ZHJ0125/FrequencyMeter/Image/00_频率计原理.jpg

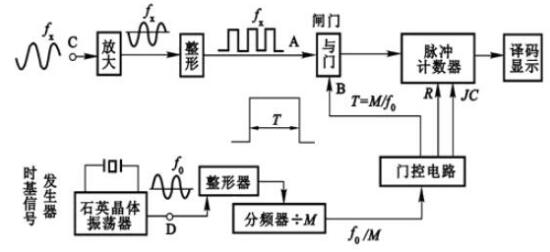
Image/00_频率计原理.jpg
