ZHJ0125/FrequencyMeter/Image/38_编译错误.png

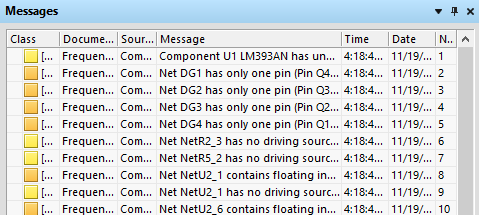
Image/38_编译错误.png
