ZHJ0125/FrequencyMeter/Image/95_生成PDF.png

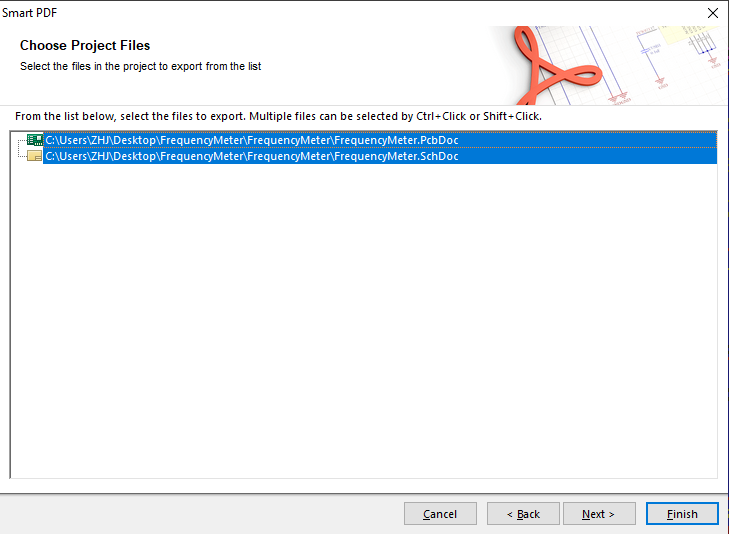
Image/95_生成PDF.png
