ZHJ0125/FrequencyMeter/Image/96_生成原理图PDF.png

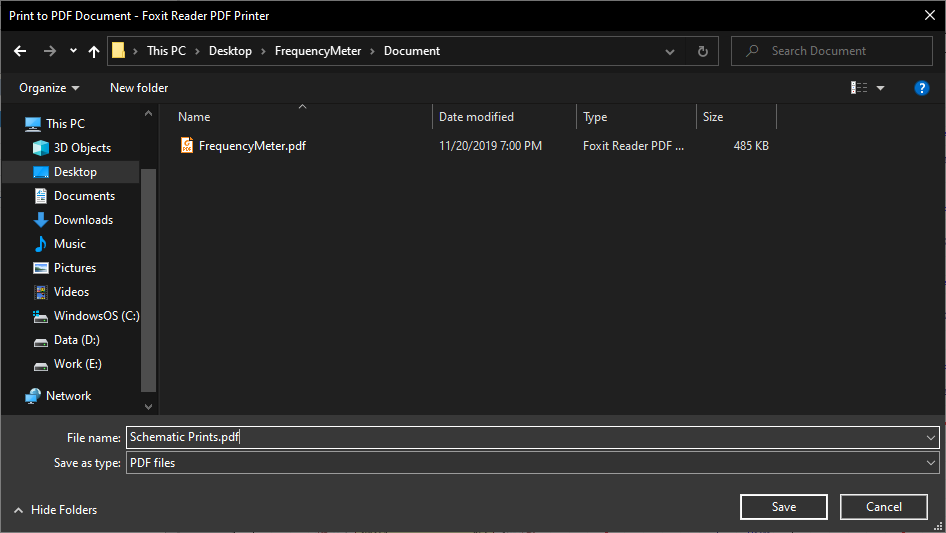
Image/96_生成原理图PDF.png
