ZHJ0125/FrequencyMeter/Image/98_文件规格.png

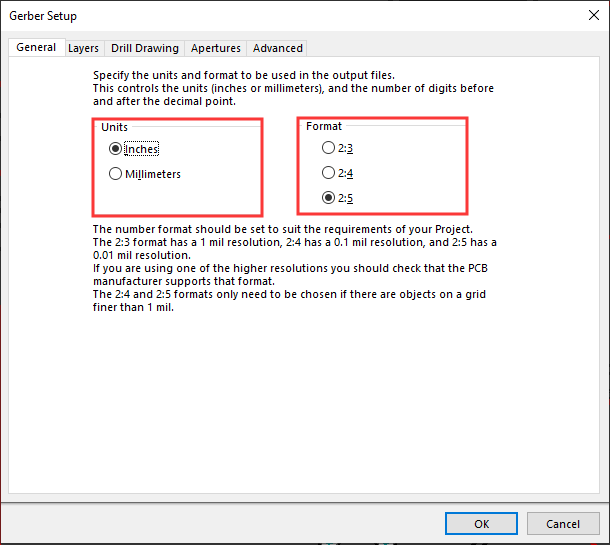
Image/98_文件规格.png
