ZHJ0125/FrequencyMeter/Image/99_版层输出.png

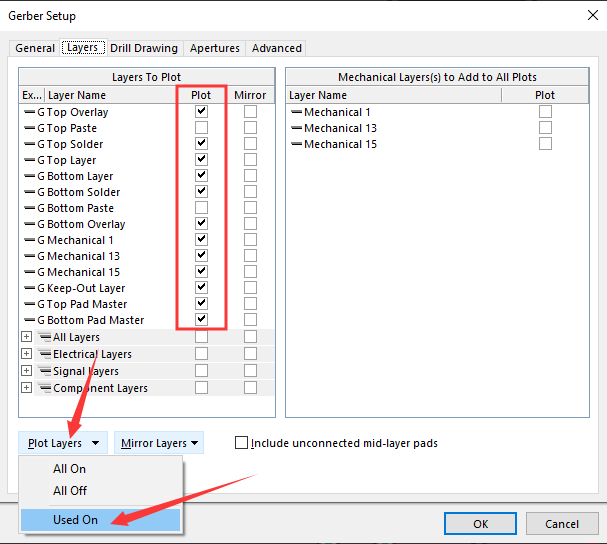
Image/99_版层输出.png
