ZHJ0125/FrequencyMeter/Image/100_输出设置.png

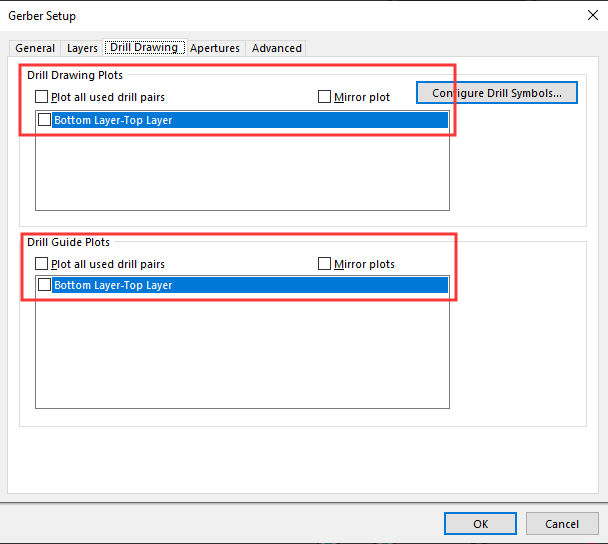
Image/100_输出设置.png
