ZHJ0125/FrequencyMeter/Image/101_嵌入式孔径.png

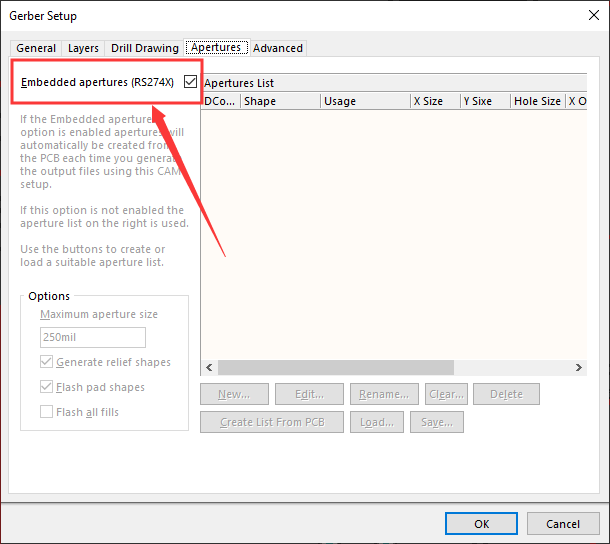
Image/101_嵌入式孔径.png
