ZHJ0125/FrequencyMeter/Image/102_高级设置.png

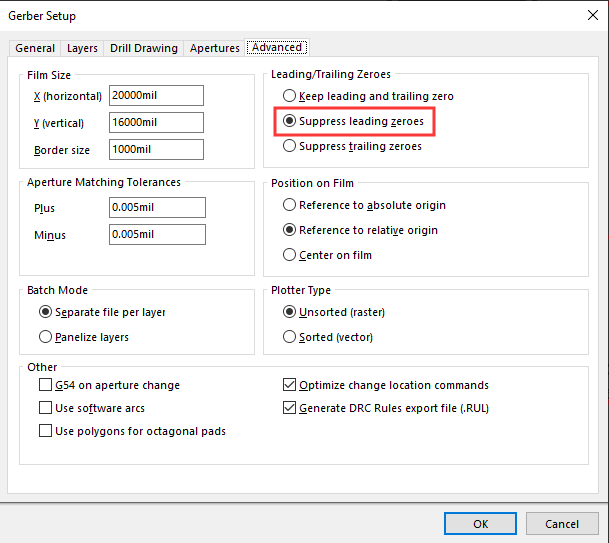
Image/102_高级设置.png
