ZHJ0125/FrequencyMeter/Image/103_cam文件.png

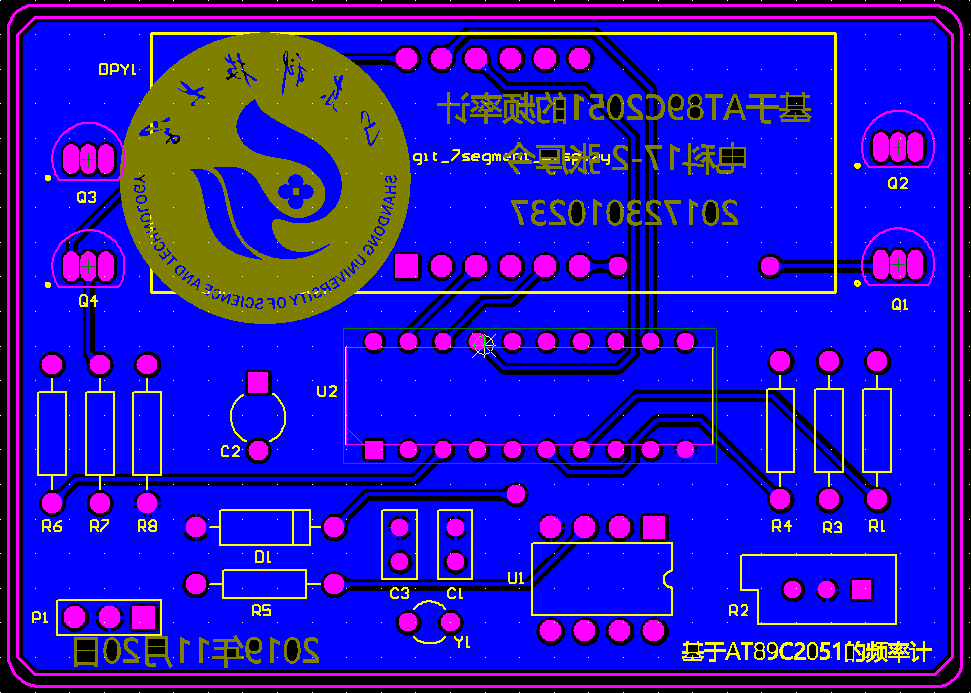
Image/103_cam文件.png
