ZHJ0125/FrequencyMeter/Image/104_Gerber文件.png

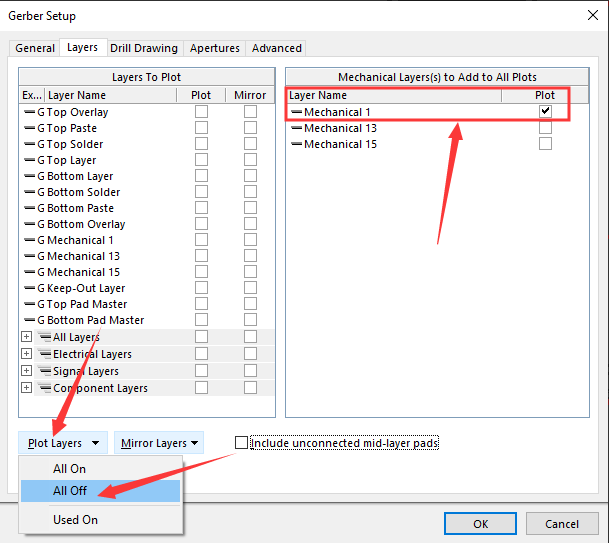
Image/104_Gerber文件.png
