ZHJ0125/FrequencyMeter/Image/105_钻孔设置.png

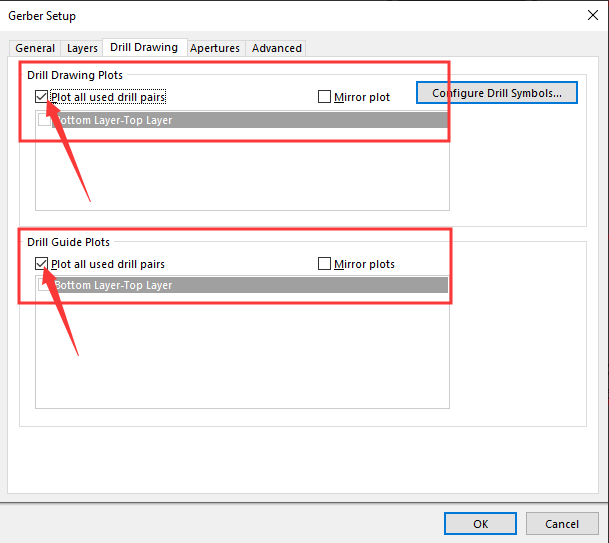
Image/105_钻孔设置.png
