ZHJ0125/FrequencyMeter/Image/106_孔位置文件.png

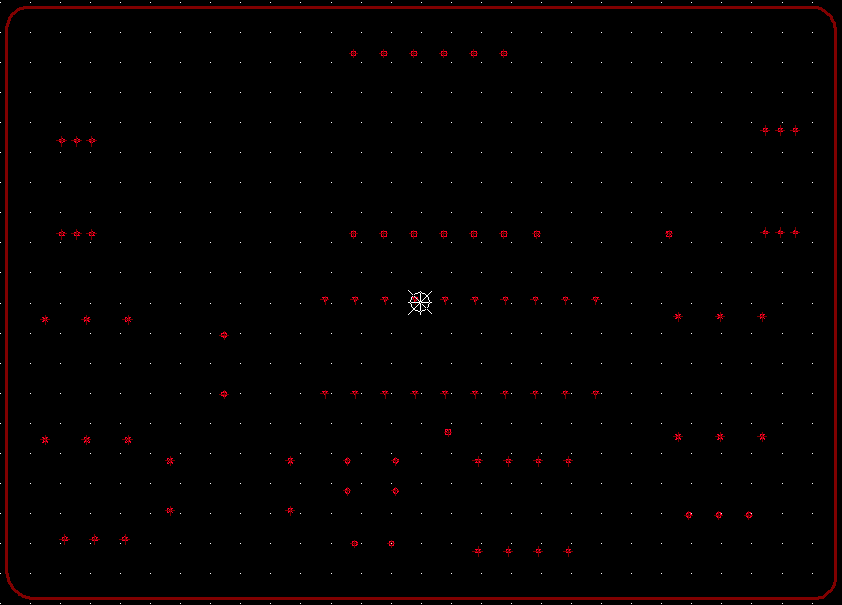
Image/106_孔位置文件.png
