ZHJ0125/FrequencyMeter/Image/107_钻孔文件.png

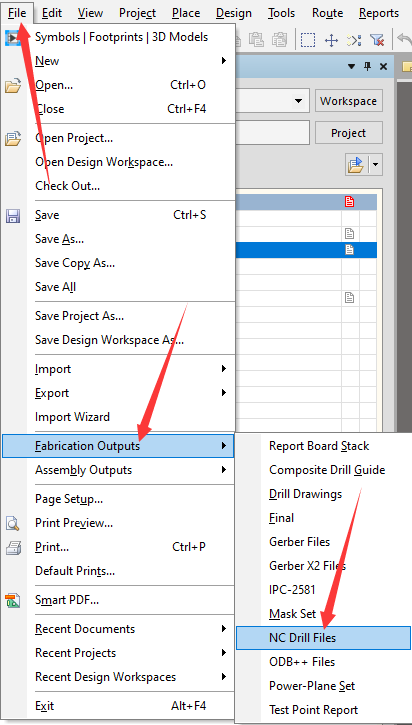
Image/107_钻孔文件.png
