ZHJ0125/FrequencyMeter/Image/108_钻孔属性设置.png

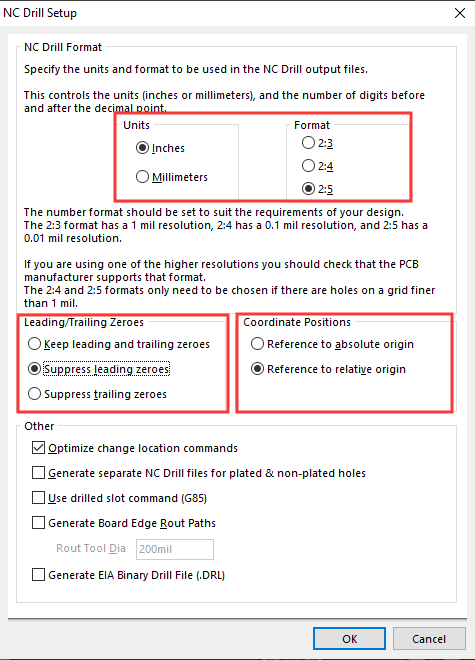
Image/108_钻孔属性设置.png
