ZHJ0125/FrequencyMeter/Image/109_钻孔属性.png

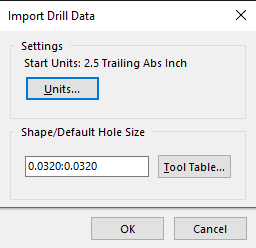
Image/109_钻孔属性.png
