ZHJ0125/FrequencyMeter/Image/110_钻孔文件.png

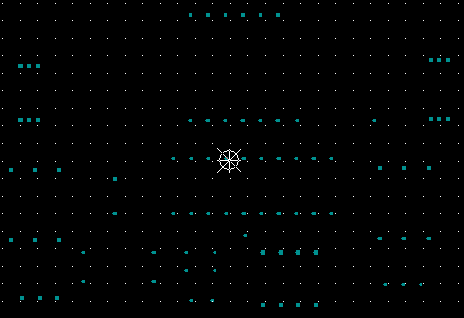
Image/110_钻孔文件.png
