ZHJ0125/FrequencyMeter/Image/111_项目目录结构.png

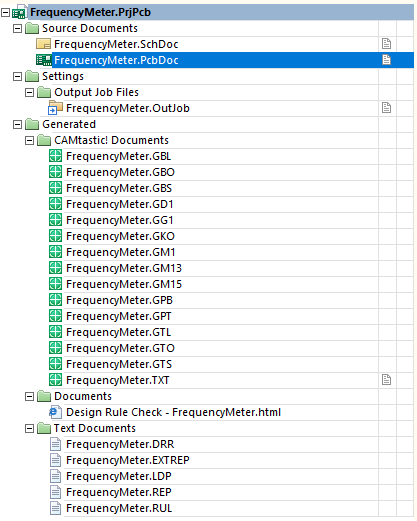
Image/111_项目目录结构.png
