ZHJ0125/FrequencyMeter/Image/112_下单界面.png

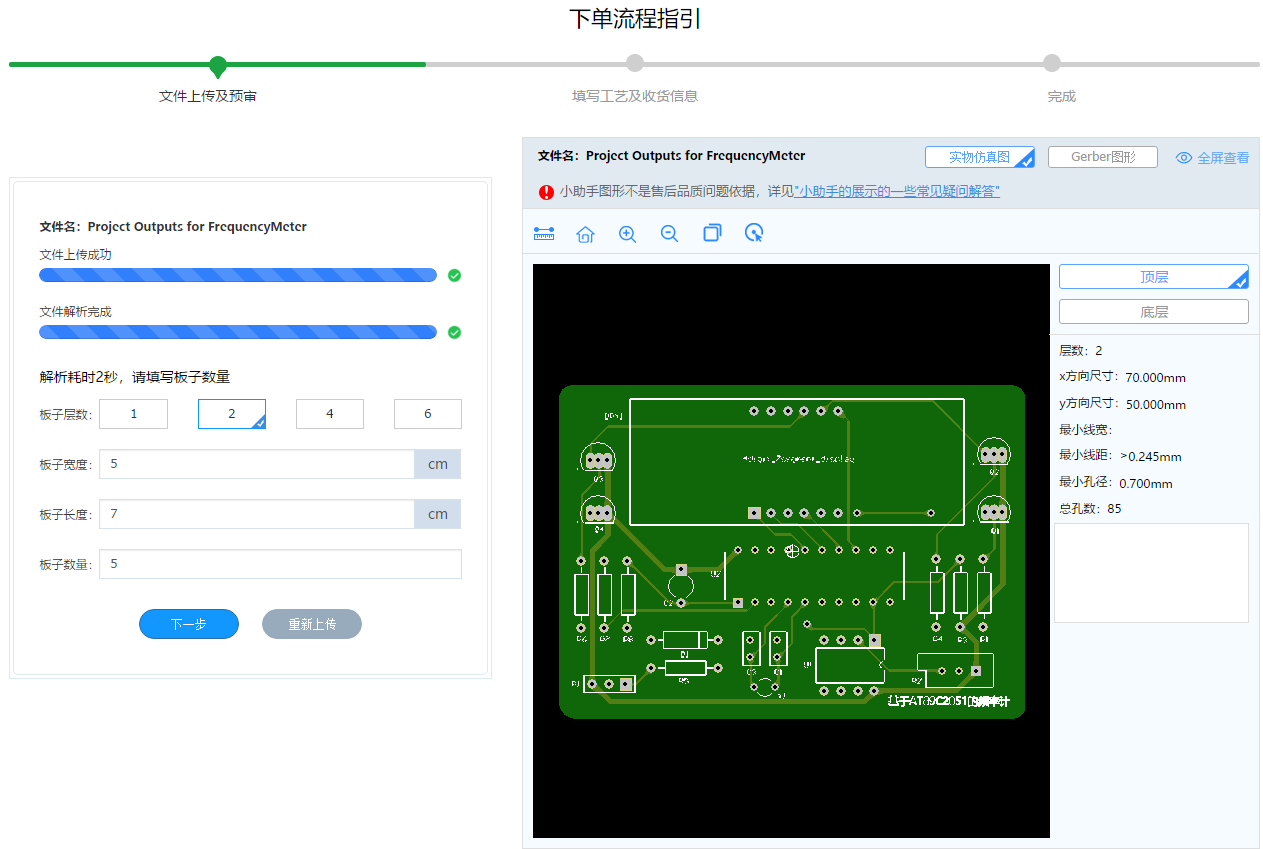
Image/112_下单界面.png
