ZHJ0125/FrequencyMeter/Image/113_下单啦.png

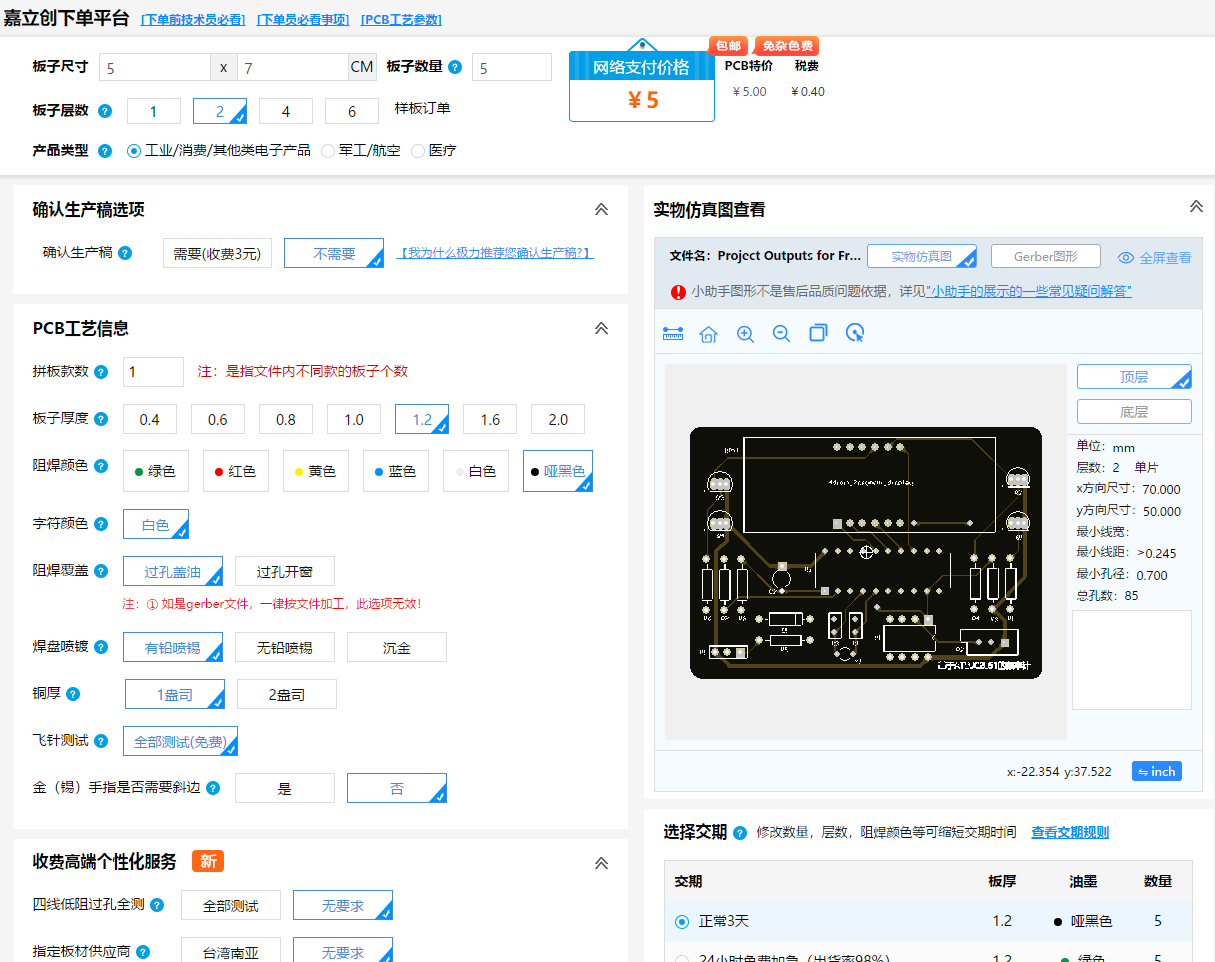
Image/113_下单啦.png
