ZHJ0125/FrequencyMeter/Image/117_表头选项.png

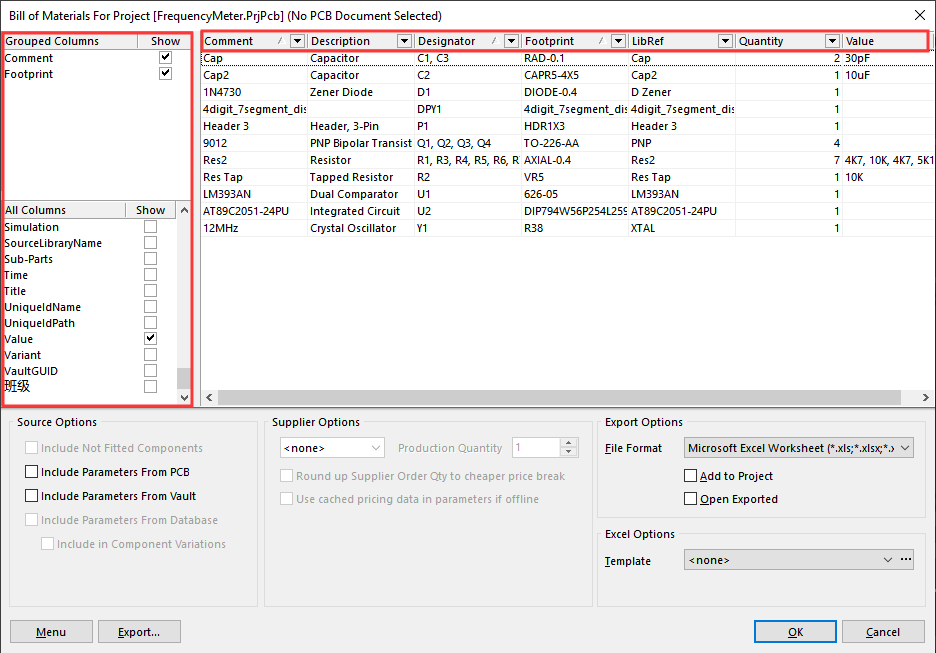
Image/117_表头选项.png
