ZHJ0125/FrequencyMeter/Image/123频率采集模块.png

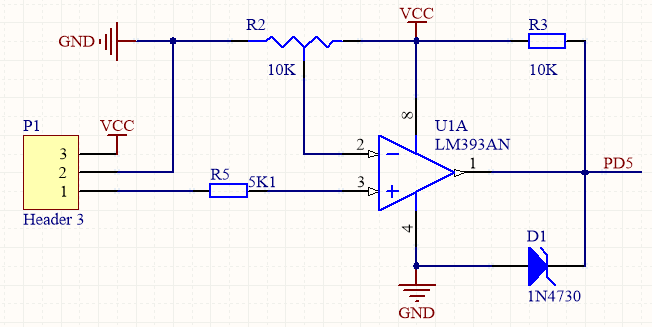
Image/123频率采集模块.png
