ZHJ0125/FrequencyMeter/Image/116_生成bom.png

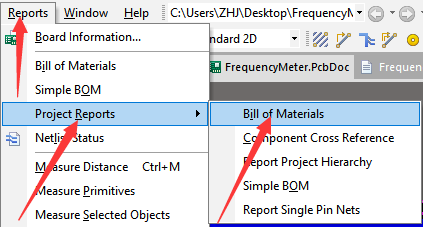
Image/116_生成bom.png
