ZHJ0125/FrequencyMeter/Image/118_BOM表内容.png

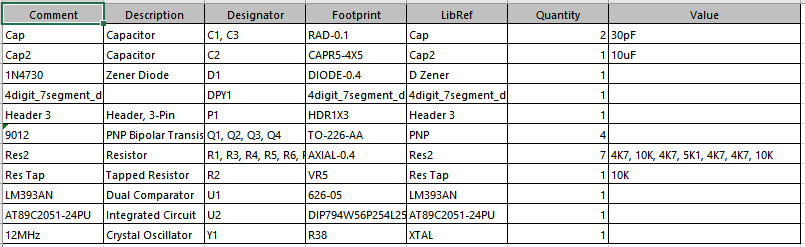
Image/118_BOM表内容.png
